timmmmimmm/VRS_Mouse_App/cad_mouse_vrs/Core/Src/i2c.c

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
/* Includes ------------------------------------------------------------------*/
#include "i2c.h"

/* USER CODE BEGIN 0 */
I2C_HandleTypeDef hi2c1;
/* USER CODE END 0 */

/* I2C1 init function */    ///////////////////////   LL FN  OLD   //////////////////////////


/////////////////////////////////            HAL FN NEW   ///////////////////////////////////

void MX_I2C1_Init(void)
{


	hi2c1.Instance = I2C1;
	hi2c1.Init.Timing = 0x0000020B;
	hi2c1.Init.OwnAddress1 = 0;
	hi2c1.Init.AddressingMode = I2C_ADDRESSINGMODE_7BIT;
	hi2c1.Init.DualAddressMode = I2C_DUALADDRESS_DISABLE;
	hi2c1.Init.OwnAddress2 = 0;
	hi2c1.Init.OwnAddress2Masks = I2C_OA2_NOMASK;
	hi2c1.Init.GeneralCallMode = I2C_GENERALCALL_DISABLE;
	hi2c1.Init.NoStretchMode = I2C_NOSTRETCH_DISABLE;
	if (HAL_I2C_Init(&hi2c1) != HAL_OK)
	{
	Error_Handler();
	}

	/** Configure Analogue filter
	*/
	if (HAL_I2CEx_ConfigAnalogFilter(&hi2c1, I2C_ANALOGFILTER_ENABLE) != HAL_OK)
	{
	Error_Handler();
	}

	/** Configure Digital filter
	*/
	if (HAL_I2CEx_ConfigDigitalFilter(&hi2c1, 0) != HAL_OK)
	{
	Error_Handler();
	}
}


/* USER CODE BEGIN 1 */

///////////////////////////         NEW WRITE FN      ////////////////////////////////////////////////////

HAL_StatusTypeDef i2c_master_write(uint8_t slave_addr, uint8_t *data, uint8_t len)
{
	return HAL_I2C_Master_Transmit_DMA(&hi2c1, slave_addr, data, len);
}



///////////////////////////         NEW READ FN      ////////////////////////////////////////////////////

HAL_StatusTypeDef i2c_master_read(uint8_t slave_addr, uint8_t *data, uint8_t len)
{
	return HAL_I2C_Master_Receive_DMA(&hi2c1, slave_addr, data, len);
}


/* USER CODE END 1 */
